mateuszkowalczyk0305/Smart_Flowerpot/LTspice/doniczka_lt_symulacja.asc

C1: cap; 100n
C2: cap; 1µ
D1: LED; NSPW500BS
M2: nmos; IRF6201
R1: res; 1k
R2: res; 10k
R3: res; 10k
R4: res; 100
R5: res; 10k
R6: res; 1k
R: res; 7k
TL081: TL081
U1: NE555
V1: voltage; 5; Rser=1m
V2: voltage; 12; Rser=1m
Named nets: 0, VCC, OUT
.tran .05
.step param R list 5k 10k 25k
